JMD-iogo/LARA_R211_BMX055_FIREBASE_Publico/circuito/circuito1.kicad_sch

## KiCad design circuito/circuito1.kicad_sch (2025-06-18)

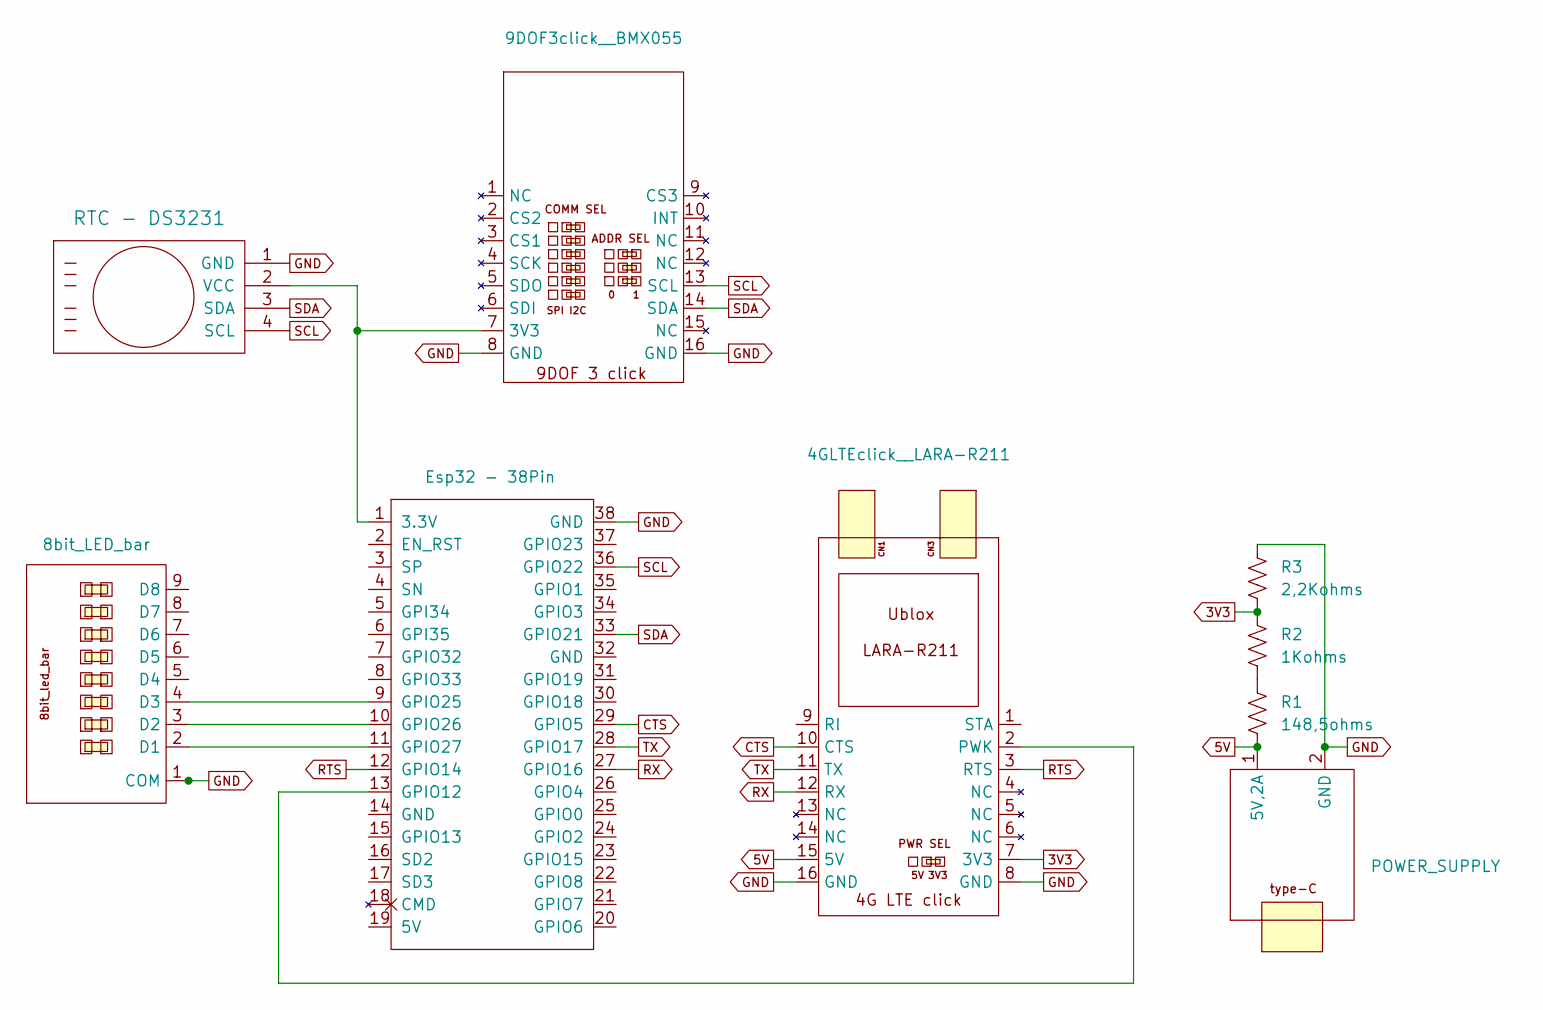
[picture p8: schematic circuito1.kicad_sch]

Parts:
4GLTEclick__LARA-R211, 8bit_LED_bar, 9DOF3click__BMX055: (no value)
Esp32 - 38Pin: (no value)
POWER_SUPPLY: (no value)
R1: 148,5ohms
R2: 1Kohms
R3: 2,2Kohms

Connections:
3V3: 4GLTEclick__LARA-R211.7 (3V3), R2.1, R3.2
5V: 4GLTEclick__LARA-R211.15 (5V), POWER_SUPPLY.1 (5V,2A), R1.2
CTS: 4GLTEclick__LARA-R211.10 (CTS), Esp32 - 38Pin.29 (GPIO5)
GND: 4GLTEclick__LARA-R211.8 (GND), 4GLTEclick__LARA-R211.16 (GND), 8bit_LED_bar.1 (COM), 9DOF3click__BMX055.8 (GND), 9DOF3click__BMX055.16 (GND), Esp32 - 38Pin.38 (GND), POWER_SUPPLY.2 (GND), R3.1
unnamed: 4GLTEclick__LARA-R211.2 (PWK), Esp32 - 38Pin.13 (GPIO12)
unnamed: 8bit_LED_bar.2 (D1), Esp32 - 38Pin.11 (GPIO27)
unnamed: 8bit_LED_bar.3 (D2), Esp32 - 38Pin.10 (GPIO26)
unnamed: 8bit_LED_bar.4 (D3), Esp32 - 38Pin.9 (GPIO25)
unnamed: 9DOF3click__BMX055.7 (3V3), Esp32 - 38Pin.1 (3.3V)
unnamed: R1.1, R2.2
RTS: 4GLTEclick__LARA-R211.3 (RTS), Esp32 - 38Pin.12 (GPIO14)
RX: 4GLTEclick__LARA-R211.12 (RX), Esp32 - 38Pin.27 (GPIO16)
SCL: 9DOF3click__BMX055.13 (SCL), Esp32 - 38Pin.36 (GPIO22)
SDA: 9DOF3click__BMX055.14 (SDA), Esp32 - 38Pin.33 (GPIO21)
TX: 4GLTEclick__LARA-R211.11 (TX), Esp32 - 38Pin.28 (GPIO17)
